Fantastair/Serial-Port-Lenses/Firmware/Core/Src/serial.c

#include "main.h"
#include "serial.h"

#define SERIAL_RX_BUFFER_SIZE 32
 
uint8_t Serial1_RxBuffer[SERIAL_RX_BUFFER_SIZE];
uint8_t Serial2_RxBuffer[SERIAL_RX_BUFFER_SIZE];
uint8_t Serial3_RxBuffer[SERIAL_RX_BUFFER_SIZE];
  
